owl-and-goat/coil-winder/parts/coil winder - z motor bracket.stl

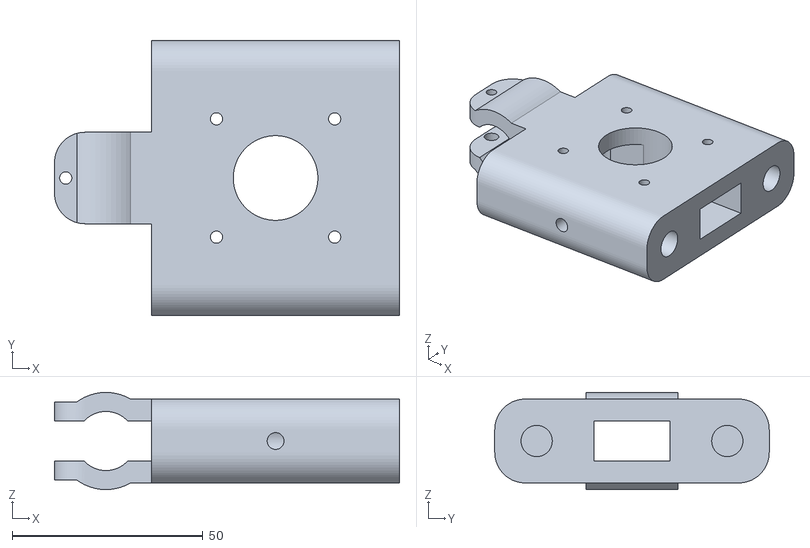
[picture p17: CAD file, 2025-11-23]
parts/coil winder - z motor bracket.stl
90.5 x 72.0 x 25.5
