owl-and-goat/coil-winder/parts/coil winder - jaw.stl

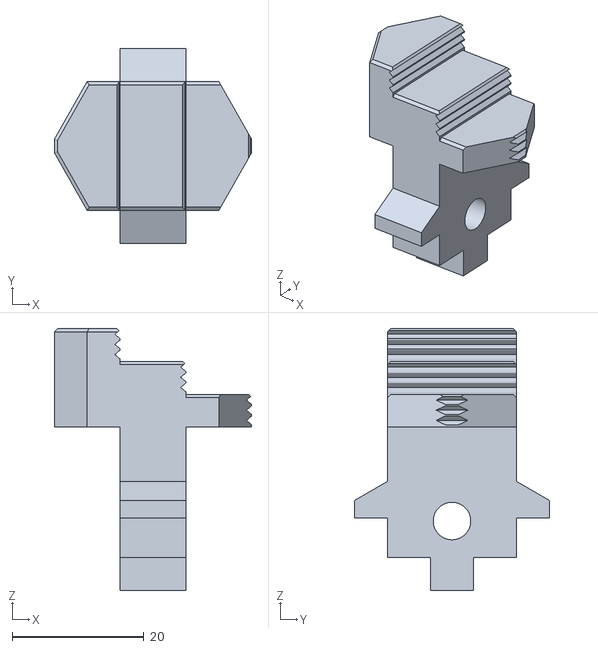
[picture p18: CAD file, 2025-11-23]
parts/coil winder - jaw.stl
30.0 x 29.6 x 39.8
