owl-and-goat/coil-winder/firmware/src/server.rs

use defmt::{debug, info, warn};
use embassy_futures::select::{Either, select};
use embassy_net::tcp::TcpSocket;
use embassy_rp::watchdog::Watchdog;
use embassy_sync::{blocking_mutex::raw::CriticalSectionRawMutex, channel};
use embassy_time::Duration;
use embedded_io_async::Write;

use crate::{AXES, AXIS_LABELS, COMMAND_BUFFER_SIZE, CommandId, MotionStatusMsg, PORT};

pub struct Server {
    pub stack: embassy_net::Stack<'static>,
    pub command_tx: channel::Sender<
        'static,
        CriticalSectionRawMutex,
        (CommandId, gcode::Command<AXES>),
        COMMAND_BUFFER_SIZE,
    >,
    pub status_rx:
        channel::Receiver<'static, CriticalSectionRawMutex, MotionStatusMsg, COMMAND_BUFFER_SIZE>,
    pub command_id_gen: u32,
    pub watchdog: Watchdog,
}

impl Server {
    fn gen_command_id(&mut self) -> CommandId {
        self.command_id_gen += 1;
        CommandId(self.command_id_gen)
    }

    pub async fn run(mut self) -> ! {
        let mut rx_buffer = [0; 1024];
        let mut tx_buffer = [0; 1024];
        let mut buf = [0; 2048];

        'accept: loop {
            let mut socket = TcpSocket::new(self.stack, &mut rx_buffer, &mut tx_buffer);
            let mut n = 0;
            socket.set_timeout(Some(Duration::from_secs(10)));

            debug!("accepting connection...");
            if let Err(e) = socket.accept(PORT).await {
                warn!("accept error: {}", e);
                continue;
            }
            info!(
                "Accepted new connection from {:?}",
                socket.remote_endpoint()
            );

            loop {
                if !socket.may_recv() {
                    info!("Remote endpoint closed connection");
                    continue 'accept;
                }
                info!("Waiting for next event...");
                match select(
                    // TODO: Ideally, this would use wait_read_ready() instead, but then we have no
                    // way of noticing that the socket has been closed (this is an embassy bug!)
                    socket.read(&mut buf[n..]),
                    self.status_rx.receive(),
                )
                .await
                {
                    Either::Second(MotionStatusMsg::CommandFinished(CommandId(id))) => {
                        debug!("Sending status message (finished #{})", id);
                        let mut done = [0u8; 64];
                        {
                            use embedded_io::Write;
                            writeln!(&mut done[..], "(done {id})").unwrap();
                        }
                        if let Err(e) = socket.write_all(&done).await {
                            warn!("write error: {}", e);
                        }
                    }
                    Either::First(Err(err)) => {
                        warn!("read error: {}", err);
                        continue 'accept;
                    }
                    Either::First(Ok(read)) => {
                        n += read;
                        debug!("reading command, starting at {}", n);
                        let command = {
                            'read_command: loop {
                                match gcode::parse_single_command(AXIS_LABELS, &buf[..n]) {
                                    Ok((remaining, command)) => {
                                        info!("Got command: {:a}", &buf[..n]);
                                        let start = usize::try_from(unsafe {
                                            remaining.as_ptr().offset_from(buf.as_ptr())
                                        })
                                        .unwrap();
                                        let end = start + remaining.len();
                                        let len = remaining.len();
                                        buf.copy_within(start..end, 0);
                                        n = len;
                                        break 'read_command command;
                                    }
                                    Err(gcode::Error::Incomplete(_)) => { /* keep reading */ }
                                    Err(gcode::Error::ParseFailed) => {
                                        warn!("parse failed: {:a}", &buf[..n]);
                                        if let Err(e) = socket.write_all(b"(parse failed)!\n").await
                                        {
                                            warn!("write error: {}", e);
                                            continue 'accept;
                                        }
                                        continue 'accept;
                                    }
                                };

                                let read = match socket.read(&mut buf[n..]).await {
                                    Ok(0) => {
                                        warn!("read EOF");
                                        continue 'accept;
                                    }
                                    Ok(n) => n,
                                    Err(e) => {
                                        warn!("read error: {}", e);
                                        continue 'accept;
                                    }
                                };
                                n += read;
                            }
                        };

                        let command_id = self.gen_command_id();
                        let mut resp_buf = [0u8; 64];
                        use embedded_io::Write;
                        writeln!(&mut resp_buf[..], "(ack {})", command_id.0).unwrap();

                        if let Err(e) = socket.write_all(&resp_buf).await {
                            warn!("write error: {}", e);
                        }

                        match command {
                            gcode::Command::ForceStop => {
                                resp_buf.fill(0);
                                writeln!(&mut resp_buf[..], "(done {})", command_id.0).unwrap();

                                if let Err(e) = socket.write_all(&resp_buf).await {
                                    warn!("write error: {}", e);
                                }

                                if let Err(e) = socket.flush().await {
                                    warn!("flush error: {}", e);
                                }

                                socket.close();

                                // XXX(nausicaa): this sure as hell stops it lol
                                self.watchdog.trigger_reset();
                            }

                            gcode::Command::Stop => {
                                self.command_tx.clear();
                                self.command_tx
                                    .send((command_id, gcode::Command::Stop))
                                    .await;
                            }

                            command => self.command_tx.send((command_id, command)).await,
                        }
                    }
                }
            }
        }
    }
}
